scottdube/hot-info-orbs/images/ClockWidget/nixie.no-holes/1.jpg

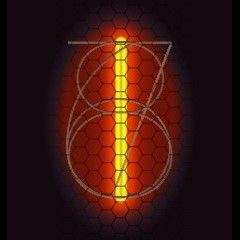
images/ClockWidget/nixie.no-holes/1.jpg
