scottdube/hot-info-orbs/images/ClockWidget/nixie.no-holes/3.jpg

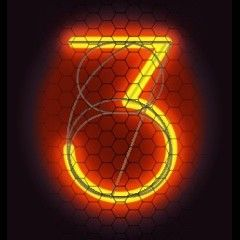
images/ClockWidget/nixie.no-holes/3.jpg
