scottdube/hot-info-orbs/images/ClockWidget/nixie.no-holes/4.jpg

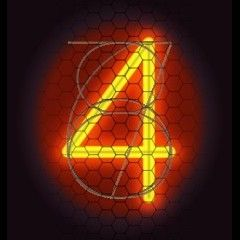
images/ClockWidget/nixie.no-holes/4.jpg
