scottdube/hot-info-orbs/images/ClockWidget/nixie.no-holes/5.jpg

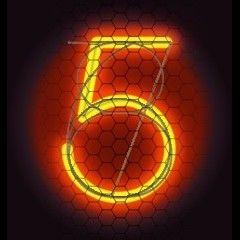
images/ClockWidget/nixie.no-holes/5.jpg
