scottdube/hot-info-orbs/images/ClockWidget/nixie.no-holes/9.jpg

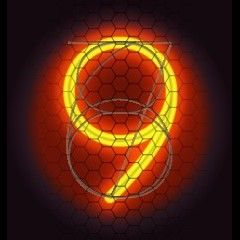
images/ClockWidget/nixie.no-holes/9.jpg
