scottdube/hot-info-orbs/PCBFiles+Schematics/Main PCB/info_orbs.kicad_sch

## KiCad design PCBFiles+Schematics/Main PCB/info_orbs.kicad_sch (2026-08-28)

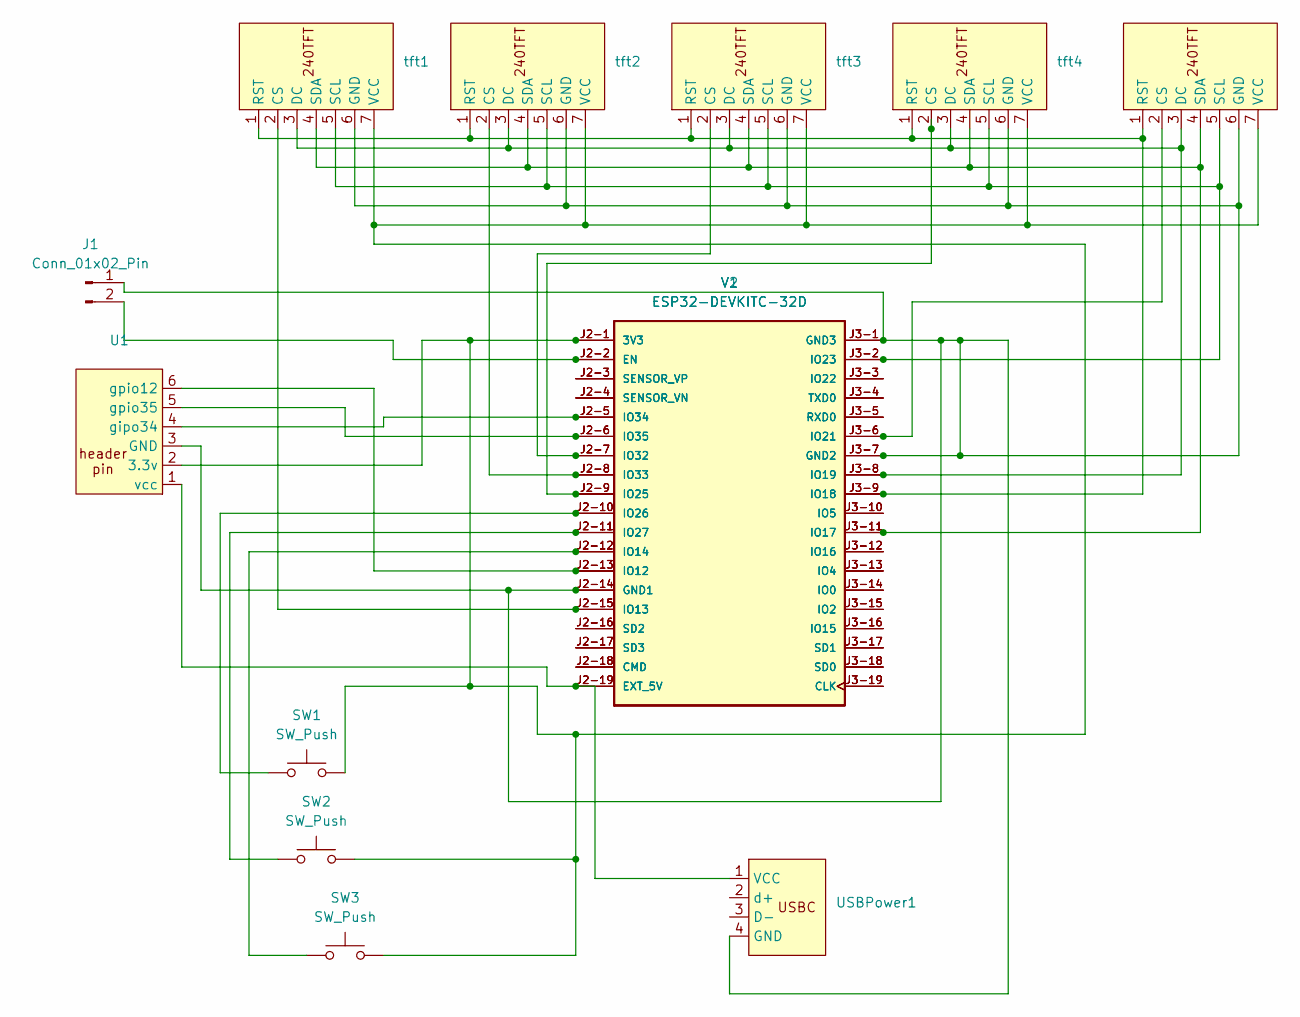
[picture p15: schematic info_orbs.kicad_sch]

Parts:
J1: Conn_01x02_Pin; PinHeader_1x02_P2.54mm_Vertical
SW1, SW2, SW3: SW_Push; SW_PUSH_6mm_H5mm
U1: PinHeader_1x06_P2.54mm_Vertical
USBPower1: PinHeader_1x04_P2.54mm_Vertical
V1: ESP32-DEVKITC-32D; 38 Pin Board; PARTREV V4
V2: ESP32-DEVKITC-32D; 38 Pin Board thin; PARTREV V4
tft1, tft2, tft3, tft4, tft5: PinHeader_1x07_P2.54mm_Vertical

Connections:
unnamed: J1.1, U1.3 (GND), USBPower1.4 (GND), V1.J2-14 (GND1), V1.J3-1 (GND3), V1.J3-7 (GND2), V2.J2-14 (GND1), V2.J3-1 (GND3), V2.J3-7 (GND2), tft1.6 (GND), tft2.6 (GND), tft3.6 (GND), tft4.6 (GND), tft5.6 (GND)
unnamed: J1.2, V1.J2-2 (EN), V2.J2-2 (EN)
unnamed: SW1.1, V1.J2-10 (IO26), V2.J2-10 (IO26)
unnamed: SW1.2, SW2.2, SW3.2, U1.2 (3.3v), V1.J2-1 (3V3), V2.J2-1 (3V3), tft1.7 (VCC), tft2.7 (VCC), tft3.7 (VCC), tft4.7 (VCC), tft5.7 (VCC)
unnamed: SW2.1, V1.J2-11 (IO27), V2.J2-11 (IO27)
unnamed: SW3.1, V1.J2-12 (IO14), V2.J2-12 (IO14)
unnamed: U1.1 (vcc), USBPower1.1 (VCC), V1.J2-19 (EXT_5V), V2.J2-19 (EXT_5V)
unnamed: U1.4 (gipo34), V1.J2-5 (IO34), V2.J2-5 (IO34)
unnamed: U1.5 (gpio35), V1.J2-6 (IO35), V2.J2-6 (IO35)
unnamed: U1.6 (gpio12), V1.J2-13 (IO12), V2.J2-13 (IO12)
unnamed: V1.J2-3 (SENSOR_VP), V2.J2-3 (SENSOR_VP)
unnamed: V1.J2-4 (SENSOR_VN), V2.J2-4 (SENSOR_VN)
unnamed: V1.J2-7 (IO32), V2.J2-7 (IO32), tft3.2 (CS)
unnamed: V1.J2-8 (IO33), V2.J2-8 (IO33), tft2.2 (CS)
unnamed: V1.J2-9 (IO25), V2.J2-9 (IO25), tft4.2 (CS)
unnamed: V1.J2-15 (IO13), V2.J2-15 (IO13), tft1.2 (CS)
unnamed: V1.J2-16 (SD2), V2.J2-16 (SD2)
unnamed: V1.J2-17 (SD3), V2.J2-17 (SD3)
unnamed: V1.J2-18 (CMD), V2.J2-18 (CMD)
unnamed: V1.J3-2 (IO23), V2.J3-2 (IO23), tft1.5 (SCL), tft2.5 (SCL), tft3.5 (SCL), tft4.5 (SCL), tft5.5 (SCL)
unnamed: V1.J3-3 (IO22), V2.J3-3 (IO22)
unnamed: V1.J3-4 (TXD0), V2.J3-4 (TXD0)
unnamed: V1.J3-5 (RXD0), V2.J3-5 (RXD0)
unnamed: V1.J3-6 (IO21), V2.J3-6 (IO21), tft5.2 (CS)
unnamed: V1.J3-8 (IO19), V2.J3-8 (IO19), tft1.3 (DC), tft2.3 (DC), tft3.3 (DC), tft4.3 (DC), tft5.3 (DC)
unnamed: V1.J3-9 (IO18), V2.J3-9 (IO18), tft1.1 (RST), tft2.1 (RST), tft3.1 (RST), tft4.1 (RST), tft5.1 (RST)
unnamed: V1.J3-10 (IO5), V2.J3-10 (IO5)
unnamed: V1.J3-11 (IO17), V2.J3-11 (IO17), tft1.4 (SDA), tft2.4 (SDA), tft3.4 (SDA), tft4.4 (SDA), tft5.4 (SDA)
unnamed: V1.J3-12 (IO16), V2.J3-12 (IO16)
unnamed: V1.J3-13 (IO4), V2.J3-13 (IO4)
unnamed: V1.J3-14 (IO0), V2.J3-14 (IO0)
unnamed: V1.J3-15 (IO2), V2.J3-15 (IO2)
unnamed: V1.J3-16 (IO15), V2.J3-16 (IO15)
unnamed: V1.J3-17 (SD1), V2.J3-17 (SD1)
unnamed: V1.J3-18 (SD0), V2.J3-18 (SD0)
unnamed: V1.J3-19 (CLK), V2.J3-19 (CLK)
