scottdube/hot-info-orbs/firmware/src/widgets/weatherwidget/WeatherWidget.cpp

// TODO:
// 1
// factor out a selectDisplay that selects the dispay and returns the workable object,
// so we don't have this select, getDisplay crap all over the place
// 2
// make high/low an enum, if we even keep it (I strongly suggest just switching back
// and forth between high and low every 10 seconds or something)
// 3
// factor out the JSON error handling (come on now)
// 4
// factor out the text wrapping (there's a utils for that already, if that doesn't work, why not?)

#include "SunMoon.h"
#include "WeatherWidget.h"
#include "icons.h"

#include "Settings.h"

WeatherWidget::WeatherWidget(ScreenManager &manager, WeatherSource *source) : Widget(manager), m_source(source) {
    m_mode = MODE_HIGHS;
    String label = m_source->label();
    if (label.length() > 0) {
        model.setCityName(label); // orb 1 names the page before the first fetch
    }
}

WeatherWidget::~WeatherWidget() {
    delete m_source;
}

void WeatherWidget::changeMode() {
    m_mode++;
    if (m_mode > MODE_LOWS) {
        m_mode = MODE_HIGHS;
    }
    threeDayWeather(4);
}

void WeatherWidget::buttonPressed(uint8_t buttonId, ButtonState state) {
    if (buttonId == BUTTON_OK && state == BTN_SHORT)
        changeMode();
}

void WeatherWidget::setup() {
    m_time = GlobalTime::getInstance();
    m_screenMode = Settings::get().wxdark ? Dark : Light;
    configureColors();
}

void WeatherWidget::draw(bool force) {
    m_manager.setFont(DEFAULT_FONT);
    m_time->updateTime();
    int clockStamp = getClockStamp();
    if (clockStamp != m_clockStamp || force) {
        displayClock(0);
        m_clockStamp = clockStamp;
    }

    if (force || model.isChanged()) {
        weatherText(1);
        // Half size (the decoder only scales by 1/2/4/8): the full-size art runs
        // y 32-205 and left no room for the sun and moon lines
        m_manager.selectScreen(2);
        m_manager.fillScreen(m_backgroundColor);
        drawWeatherIcon(2, model.getCurrentIcon(), 60, 60, 2);
        sunMoon(2);
        singleWeatherDeg(3);
        threeDayWeather(4);
        model.setChangedStatus(false);
    }
}

void WeatherWidget::update(bool force) {
    if (force || m_weatherDelayPrev == 0 || (millis() - m_weatherDelayPrev) >= m_weatherDelay) {
        setBusy(true);
        if (force) {
            int retry = 0;
            while (!m_source->fetch(model) && retry++ < MAX_RETRIES)
                ;
        } else {
            m_source->fetch(model);
        }
        setBusy(false);
        m_weatherDelayPrev = millis();
    }
}

void WeatherWidget::displayClock(int displayIndex) {
    const int clockY = 120;
    const int dayOfWeekY = 190;
    const int dateY = 50;

    m_manager.selectScreen(displayIndex);
    m_manager.fillScreen(m_backgroundColor);
    m_manager.setFontColor(m_foregroundColor);

    m_manager.drawCenterString(m_time->getDayAndMonth(), center, dateY, 18);
    const String weekDay = m_time->getWeekday();
    m_manager.drawCenterString(weekDay, center, dayOfWeekY, 22);

    m_manager.drawString(m_time->getHourPadded(), center - 10, clockY, 66, Align::MiddleRight);
    m_manager.drawString(":", center, clockY, 66, Align::MiddleCenter);
    m_manager.drawString(m_time->getMinutePadded(), center + 10, clockY, 66, Align::MiddleLeft);
}

// Write an image to the screen from a hex array.
// scale of the image (1=full size, then multiples of 2 to scale down)
// getting the byte array size is very annoying as it's computed on compile, so you can't do it dynamically.
void WeatherWidget::showJPG(int displayIndex, int x, int y, const byte jpgData[], int jpgDataSize, int scale) {
    m_manager.selectScreen(displayIndex);

    TJpgDec.setJpgScale(scale);
    uint16_t w = 0, h = 0;
    TJpgDec.getJpgSize(&w, &h, jpgData, jpgDataSize);
    TJpgDec.drawJpg(x, y, jpgData, jpgDataSize);
}

// Take the text output from the weather API and map it to a icon/byte array, then display it
void WeatherWidget::drawWeatherIcon(int displayIndex, const String &condition, int x, int y, int scale) {
    const byte *iconStart = NULL;
    const byte *iconEnd = NULL;

    if (condition == "partly-cloudy-night") {
        iconStart = m_screenMode == Light ? moonCloudW_start : moonCloudB_start;
        iconEnd = m_screenMode == Light ? moonCloudW_end : moonCloudB_end;
    } else if (condition == "partly-cloudy-day") {
        iconStart = m_screenMode == Light ? sunCloudsW_start : sunCloudsB_start;
        iconEnd = m_screenMode == Light ? sunCloudsW_end : sunCloudsB_end;
    } else if (condition == "clear-day") {
        iconStart = m_screenMode == Light ? sunW_start : sunB_start;
        iconEnd = m_screenMode == Light ? sunW_end : sunB_end;
    } else if (condition == "clear-night") {
        iconStart = m_screenMode == Light ? moonW_start : moonB_start;
        iconEnd = m_screenMode == Light ? moonW_end : moonB_end;
    } else if (condition == "snow") {
        iconStart = m_screenMode == Light ? snowW_start : snowB_start;
        iconEnd = m_screenMode == Light ? snowW_end : snowB_end;
    } else if (condition == "rain") {
        iconStart = m_screenMode == Light ? rainW_start : rainB_start;
        iconEnd = m_screenMode == Light ? rainW_end : rainB_end;
    } else if (condition == "fog" || condition == "wind" || condition == "cloudy") {
        iconStart = m_screenMode == Light ? cloudsW_start : cloudsB_start;
        iconEnd = m_screenMode == Light ? cloudsW_end : cloudsB_end;
    } else {
        Serial.println("unknown weather icon:" + condition);
    }

    const int size = iconEnd - iconStart;
    if (iconStart != NULL && size > 0) {
        showJPG(displayIndex, x, y, iconStart, size, scale);
    }
}

// Sunrise/sunset above the half-size icon and the moon phase below it. Not a
// page of its own: that would cost flash we are short of. Redrawn whenever the weather refreshes.
void WeatherWidget::sunMoon(int displayIndex) {
    m_manager.selectScreen(displayIndex);
    int offset = m_time->getTimeZoneOffset();
    bool h24 = m_time->getFormat24Hour();
    std::string rise = sunClock(model.getSunrise(), offset, h24), set = sunClock(model.getSunset(), offset, h24);
    m_manager.setFontColor(m_foregroundColor);
    if (!rise.empty() && !set.empty()) { // stacked: one line was too wide for the round top
        m_manager.drawCenterString(("Sunrise " + rise).c_str(), center, 30, 17);
        m_manager.drawCenterString(("Sunset " + set).c_str(), center, 52, 17);
    }
    int64_t utc = (int64_t)m_time->getUnixEpoch() - offset; // getUnixEpoch() is local-shifted
    drawMoon(center, 202, 20, moonAgeDays(utc));
}

// A small moon showing today's phase: pale lit part on a dark disc, outlined
// so a new moon still reads. Drawn row by row, so it costs no image flash.
// The picture replaced the phase name, which few people could decode.
void WeatherWidget::drawMoon(int cx, int cy, int r, double ageDays) {
    const uint32_t dark = 0x39E7, lit = 0xFFF6; // gray, pale yellow
    m_manager.fillCircle(cx, cy, r, dark);
    for (int dy = -r; dy <= r; dy++) {
        double w = std::sqrt((double)(r * r - dy * dy)), x0, x1;
        moonLitSpan(ageDays, w, x0, x1);
        int a = (int)std::lround(x0), b = (int)std::lround(x1);
        if (b > a) {
            m_manager.fillRect(cx + a, cy + dy, b - a, 1, lit);
        }
    }
    m_manager.drawCircle(cx, cy, r, m_foregroundColor);
}

// Displays the current temperature on a single screen.
// doesn't round deg, just removes all text after the decimal
void WeatherWidget::singleWeatherDeg(int displayIndex) {
    m_manager.selectScreen(displayIndex);
    m_manager.fillScreen(m_backgroundColor);
    m_manager.drawCenterString(model.getCurrentTemperature(0), center, 90, 88);

    // No glaring white chunks in Dark mode
    if (m_screenMode == Light) {
        m_manager.fillRect(0, 150, 240, 90, m_foregroundColor);
        m_manager.fillRect(center - 1, 150, 2, 90, m_backgroundColor);
    }

    int fontSize = 22;
    m_manager.setFontColor(m_invertedForegroundColor);
    m_manager.setBackgroundColor(m_invertedBackgroundColor);
    m_manager.drawCenterString("High", 80, 170, fontSize);
    m_manager.drawCenterString("Low", 160, 170, fontSize);
    m_manager.drawCenterString(model.getTodayHigh(0), 80, 210, fontSize);
    m_manager.drawCenterString(model.getTodayLow(0), 160, 210, fontSize);
    m_manager.setFontColor(m_foregroundColor);
    m_manager.setBackgroundColor(m_backgroundColor);
}

// Display the user's current city and the text description of the weather
void WeatherWidget::weatherText(int displayIndex) {
    m_manager.selectScreen(displayIndex);

    //=== TEXT OVERFLOW ============================
    // This takes a given string a and breaks it down in max x character long strings ensuring not to break it only at a space.
    // Given the small width of the screens this will porbablly be needed to this project again so making sure to outline it
    // clearly as this should liekly eventually be turned into a fucntion. Before use the array size should be made to be dynamic.
    // In this case its used for the weather text description

    String message = model.getCurrentText() + " ";
    String messageArr[4];
    if (message.indexOf('\n') >= 0) {
        // Already laid out one line per reading (Tempest's station readings)
        int start = 0;
        for (int i = 0; i < 4 && start < (int)message.length(); i++) {
            int nl = message.indexOf('\n', start);
            messageArr[i] = message.substring(start, nl < 0 ? message.length() : nl);
            start = nl < 0 ? message.length() : nl + 1;
        }
    } else {
        int variableRangeS = 0;
        int variableRangeE = 18;
        for (int i = 0; i < 4; i++) {
            while (message.substring(variableRangeE - 1, variableRangeE) != " ") {
                variableRangeE--;
            }
            messageArr[i] = message.substring(variableRangeS, variableRangeE);
            variableRangeS = variableRangeE;
            variableRangeE = variableRangeS + 18;
        }
    }
    //=== OVERFLOW END ==============================

    m_manager.fillScreen(m_backgroundColor);
    String cityName = model.getCityName();
    cityName.remove(cityName.indexOf(",", 0));

    m_manager.setFontColor(m_foregroundColor);
    m_manager.drawFittedString(cityName, center, 80, 210, 50, Align::MiddleCenter);

    auto y = 125;
    for (auto i = 0; i < 4; i++) {
        m_manager.drawCenterString(messageArr[i], center, y, 15);
        y += 25;
    }
}

// Displays the next 3 days' weather forecast
void WeatherWidget::threeDayWeather(int displayIndex) {
    const int days = 3;
    const int columnSize = 75;
    const int highLowY = 210;

    m_manager.selectScreen(displayIndex);
    m_manager.fillScreen(m_backgroundColor);
    int fontSize = 22;

    // No glaring white chunks in Dark mode
    if (m_screenMode == Light) {
        m_manager.fillRect(0, 180, 240, 70, m_foregroundColor);
    }

    m_manager.drawString(m_mode == MODE_HIGHS ? "Highs" : "Lows", center, highLowY, fontSize, Align::MiddleCenter, m_invertedForegroundColor, m_invertedBackgroundColor);
    // Reset colors
    m_manager.setFontColor(m_foregroundColor);
    m_manager.setBackgroundColor(m_backgroundColor);

    int temperatureFontSize = fontSize; // 0-9 only
    // Look up all the temperatures, and if any of them are more than 2 digits, we need
    // to scale down the font -- or it won't look right on the screen.
    String temps[days];
    for (auto i = 0; i < days; i++) {
        temps[i] = m_mode == MODE_HIGHS ? model.getDayHigh(i, 0) : model.getDayLow(i, 0);
        if (temps[i].length() > 4) {
            // We've got a nutty 3-digit temperature (plus degree sign), scale down
            temperatureFontSize = fontSize - 4; // smaller
        }
    }

    m_manager.setFontColor(m_foregroundColor);
    for (auto i = 0; i < days; i++) {
        // TODO: only works for 3 days
        const int x = (center - columnSize) + i * columnSize;

        drawWeatherIcon(displayIndex, model.getDayIcon(i), x - 30, 40, 4);
        m_manager.drawCenterString(temps[i], x, 122, temperatureFontSize);

        String shortDayName = LOC_WEEKDAY[weekday(m_time->getUnixEpoch() + (86400 * (i + 1))) - 1];
        shortDayName.remove(3);
        m_manager.drawString(shortDayName, x, 154, fontSize, Align::MiddleCenter);
    }
}

int WeatherWidget::getClockStamp() {
    return m_time->getHour() * 60 + m_time->getMinute();
}

void WeatherWidget::configureColors() {
    m_foregroundColor = m_screenMode == Light ? TFT_BLACK : TFT_WHITE;
    m_backgroundColor = m_screenMode == Light ? TFT_WHITE : TFT_BLACK;

    // NOTE: In Light mode, we draw decorative black chunks and display the high and low on them in white.
    //       It does not make sense to have glaring white chunks in dark mode, so we don't draw them at all,
    //       and display the high and low in white too.
    m_invertedForegroundColor = m_screenMode == Light ? m_backgroundColor : m_foregroundColor;
    m_invertedBackgroundColor = m_screenMode == Light ? m_foregroundColor : m_backgroundColor;

    m_manager.setBackgroundColor(m_backgroundColor);
}

String WeatherWidget::getName() {
    return m_source->name();
}
