scottdube/hot-info-orbs/firmware/src/core/globaltime/GlobalTime.cpp

#include "GlobalTime.h"
#include "SettingsValidation.h"

#include "config_helper.h"
#include <TimeLib.h>

GlobalTime *GlobalTime::m_instance = nullptr;

GlobalTime::GlobalTime() {
    m_timeClient = new NTPClient(m_udp);
    m_timeClient->begin();
    m_timeClient->setPoolServerName(NTP_SERVER);
}

GlobalTime::~GlobalTime() {
    delete m_timeClient;
}

GlobalTime *GlobalTime::getInstance() {
    if (m_instance == nullptr) {
        m_instance = new GlobalTime();
    }
    return m_instance;
}

void GlobalTime::updateTime() {
    if (millis() - m_updateTimer > m_oneSecond) {
        if (m_timeZoneOffset == -1 || (m_nextTimeZoneUpdate > 0 && m_unixEpoch > m_nextTimeZoneUpdate)) {
            getTimeZoneOffsetFromAPI();
        }
        m_timeClient->update();
        m_unixEpoch = m_timeClient->getEpochTime();
        m_updateTimer = millis();
        m_minute = minute(m_unixEpoch);
        if (m_format24hour) {
            m_hour = hour(m_unixEpoch);
        } else {
            m_hour = hourFormat12(m_unixEpoch);
        }
        m_hour24 = hour(m_unixEpoch);
        m_second = second(m_unixEpoch);

        m_day = day(m_unixEpoch);
        m_month = month(m_unixEpoch);
        m_monthName = LOC_MONTH[m_month - 1];
        m_year = year(m_unixEpoch);
        m_weekday = LOC_WEEKDAY[(weekday(m_unixEpoch)) -1];
        m_time = String(m_hour) + ":" + (m_minute < 10 ? "0" + String(m_minute) : String(m_minute));
    }
}

void GlobalTime::getHourAndMinute(int &hour, int &minute) {
    hour = m_hour;
    minute = m_minute;
}

int GlobalTime::getHour() {
    return m_hour;
}

int GlobalTime::getHour24() {
    return m_hour24;
}

String GlobalTime::getHourPadded() {
    if (m_hour < 10) {
        return "0" + String(m_hour);
    } else {
        return String(m_hour);
    }
}

int GlobalTime::getMinute() {
    return m_minute;
}

String GlobalTime::getMinutePadded() {
    if (m_minute < 10) {
        return "0" + String(m_minute);
    } else {
        return String(m_minute);
    }
}

int GlobalTime::getSecond() {
    return m_second;
}

time_t GlobalTime::getUnixEpoch() {
    return m_unixEpoch;
}

int GlobalTime::getDay() {
    return m_day;
}

int GlobalTime::getMonth() {
    return m_month;
}

String GlobalTime::getMonthName() {
    return m_monthName;
}

int GlobalTime::getYear() {
    return m_year;
}

String GlobalTime::getTime() {
    return m_time;
}

String GlobalTime::getWeekday() {
    return m_weekday;
}

String GlobalTime::getDayAndMonth() {
    if (Settings::get().wxmetric) {
        String retVal = LOC_FORMAT_DAYMONTH;
        retVal.replace("%d", String(m_day));
        retVal.replace("%B", m_monthName);
        return retVal;
    }
    return m_monthName + " " + String(m_day);
}

#include <HTTPClient.h> // Include the necessary header file

bool GlobalTime::isPM() {
    return hour(m_unixEpoch) >= 12;
}

void GlobalTime::getTimeZoneOffsetFromAPI() {
    HTTPClient http;
    http.begin(String(TIMEZONE_API_URL) + "?key=" + TIMEZONE_API_KEY + "&format=json&fields=gmtOffset,zoneEnd&by=zone&zone=" + String(sv::urlEncode(Settings::get().tz).c_str()));
    int httpCode = http.GET();

    if (httpCode > 0) {
        JsonDocument doc;
        DeserializationError error = deserializeJson(doc, http.getString());
        if (!error) {
            m_timeZoneOffset = doc["gmtOffset"].as<int>();
            if (doc["zoneEnd"].isNull()) {
                // Timezone does not use DST, no futher updates necessary
                m_nextTimeZoneUpdate = 0;
            } else {
                // Timezone uses DST, update when necessary
                m_nextTimeZoneUpdate = doc["zoneEnd"].as<unsigned long>() + random(5 * 60); // Randomize update by 5 minutes to avoid flooding the API
            }
            Serial.print("Timezone Offset from API: ");
            Serial.println(m_timeZoneOffset);
            Serial.print("Next timezone update: ");
            Serial.println(m_nextTimeZoneUpdate);
            m_timeClient->setTimeOffset(m_timeZoneOffset);
        } else {
            Serial.println("Deserialization error on timezone offset API response");
        }
    } else {
        Serial.println("Failed to get timezone offset from API");
    }
}

int GlobalTime::getTimeZoneOffset() {
    return m_timeZoneOffset == -1 ? 0 : m_timeZoneOffset;
}

bool GlobalTime::getFormat24Hour() {
    return m_format24hour;
}

bool GlobalTime::setFormat24Hour(bool format24hour) {
    m_format24hour = format24hour;
    return m_format24hour;
}
