scottdube/hot-info-orbs/firmware/src/widgets/weatherwidget/WeatherWidget.h

#ifndef WEATHERWIDGET_H
#define WEATHERWIDGET_H

#include "GlobalTime.h"
#include "Utils.h"
#include "WeatherDataModel.h"
#include "WeatherSource.h"
#include "Widget.h"
#include "config_helper.h"
#include <ArduinoJson.h>
#include <HTTPClient.h>
#include <TJpg_Decoder.h>
#include <math.h>

class WeatherWidget : public Widget {
public:
    WeatherWidget(ScreenManager &manager, WeatherSource *source); // takes ownership of source
    ~WeatherWidget() override;
    void setup() override;
    void update(bool force = false) override;
    void draw(bool force = false) override;
    void buttonPressed(uint8_t buttonId, ButtonState state) override;
    String getName() override;

private:
    void displayClock(int displayIndex);
    void changeMode();
    void displayClock(int displayIndex, uint32_t background, uint32_t textColor);
    void showJPG(int displayIndex, int x, int y, const byte jpgData[], int size, int scale);
    void drawWeatherIcon(int displayIndex, const String &condition, int x, int y, int scale);
    void singleWeatherDeg(int displayIndex);
    void sunMoon(int displayIndex);
    void drawMoon(int cx, int cy, int r, double ageDays);
    void weatherText(int displayIndex);
    void threeDayWeather(int displayIndex);
    int getClockStamp();
    void configureColors();

    GlobalTime *m_time;
    int8_t m_mode;

    ScreenMode m_screenMode = Dark;
    uint16_t m_foregroundColor;
    uint16_t m_backgroundColor;
    uint16_t m_invertedForegroundColor;
    uint16_t m_invertedBackgroundColor;

    const long m_weatherDelay = 600000; // Weather refresh rate
    unsigned long m_weatherDelayPrev = 0;

    const int center = 120; // Center location of the screen(240x240)

    int m_clockStamp = 0;

    WeatherDataModel model;

    WeatherSource *m_source;

    const int MODE_HIGHS = 0;
    const int MODE_LOWS = 1;
};
#endif // WEATHERWIDGET_H
