scottdube/hot-info-orbs/firmware/src/core/utils/Utils.h

#ifndef UTILS_H
#define UTILS_H

#include <Arduino.h>
#include <TFT_eSPI.h>

#define MAX_WRAPPED_LINES 10

#define FIRMWARE_VERSION "1.1.0" // shown on the boot screen and the OTA update page

enum ScreenMode {
    Light = 1,
    Dark = 2
};

#define ScreenWidth 240
#define ScreenHeight 240
#define ScreenCenterX (ScreenWidth / 2)
#define ScreenCenterY (ScreenHeight / 2)

class Utils {
public:
    static int getWrappedLines(String (&lines)[MAX_WRAPPED_LINES], String str, int limit);
    static String getWrappedLine(String str, int limit, int lineNum, int maxLines);
    static int32_t stringToColor(String color);
    static String formatFloat(float value, int8_t digits);
    static int32_t stringToAlignment(String alignment);
    static uint16_t rgb565dim(uint16_t color, uint8_t brightness, bool swapBytes = false);
};

#endif
